velezd/pycogame/code/games/MicroMaze 3D/source/intro.png

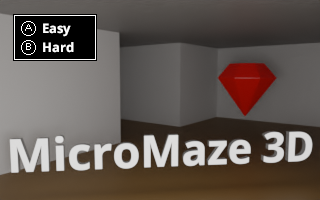
code/games/MicroMaze 3D/source/intro.png
