velezd/pycogame/code/games/MicroMaze 3D/source/graphics.png

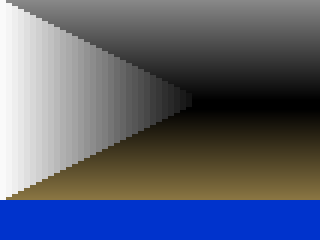
code/games/MicroMaze 3D/source/graphics.png
