velezd/pycogame/code/games/Micronoid/source/preview.png

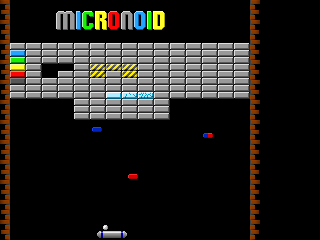
code/games/Micronoid/source/preview.png
