velezd/pycogame/code/games/MicroMaze 3D/maze.py

# -*- coding: utf-8 -*-
"""
Modified maze generator from BoppreH
https://github.com/boppreh/maze

The MIT License (MIT)

Copyright (c) 2014 BoppreH

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
# Easy to read representation for each cardinal direction.
N, S, W, E = ('n', 's', 'w', 'e')

class Cell(object):
    """
    Class for each individual cell. Knows only its position and which walls are
    still standing.
    """
    def __init__(self, x, y, walls):
        self.x = x
        self.y = y
        self.walls = set(walls)

    def __repr__(self):
        # <15, 25 (es  )>
        return '<{}, {} ({:4})>'.format(self.x, self.y, ''.join(sorted(self.walls)))

    def __contains__(self, item):
        # N in cell
        return item in self.walls

    def is_full(self):
        """
        Returns True if all walls are still standing.
        """
        return len(self.walls) == 4

    def _wall_to(self, other):
        """
        Returns the direction to the given cell from the current one.
        Must be one cell away only.
        """
        assert abs(self.x - other.x) + abs(self.y - other.y) == 1, '{}, {}'.format(self, other)
        if other.y < self.y:
            return N
        elif other.y > self.y:
            return S
        elif other.x < self.x:
            return W
        elif other.x > self.x:
            return E
        else:
            assert False

    def connect(self, other):
        """
        Removes the wall between two adjacent cells.
        """
        other.walls.remove(other._wall_to(self))
        self.walls.remove(self._wall_to(other))

class Maze(object):
    """
    Maze class containing full board and maze generation algorithms.
    """
    def __init__(self, width, height):
        """
        Creates a new maze with the given sizes, with all walls standing.
        """
        self.width = width
        self.height = height
        self.cells = []
        for y in range(self.height):
            for x in range(self.width):
                self.cells.append(Cell(x, y, [N, S, E, W]))

    def __getitem__(self, index):
        """
        Returns the cell at index = (x, y).
        """
        x, y = index
        if 0 <= x < self.width and 0 <= y < self.height:
            return self.cells[x + y * self.width]
        else:
            return None

    def neighbors(self, cell):
        """
        Returns the list of neighboring cells, not counting diagonals. Cells on
        borders or corners may have less than 4 neighbors.
        """
        x = cell.x
        y = cell.y
        for new_x, new_y in [(x, y - 1), (x, y + 1), (x - 1, y), (x + 1, y)]:
            neighbor = self[new_x, new_y]
            if neighbor is not None:
                yield neighbor

    def _to_str_matrix(self):
        """
        Returns a matrix with a pretty printed visual representation of this
        maze. Example 5x5:

        OOOOOOOOOOO
        O       O O
        OOO OOO O O
        O O   O   O
        O OOO OOO O
        O   O O   O
        OOO O O OOO
        O   O O O O
        O OOO O O O
        O     O   O
        OOOOOOOOOOO
        """
        str_matrix = [['#'] * (self.width * 2 + 1)
                      for i in range(self.height * 2 + 1)]

        for cell in self.cells:
            x = cell.x * 2 + 1
            y = cell.y * 2 + 1
            str_matrix[y][x] = '.'

            if N not in cell and y > 0:
                str_matrix[y - 1][x + 0] = '.'
            if S not in cell and y + 1 < self.width:
                str_matrix[y + 1][x + 0] = '.'
            if W not in cell and x > 0:
                str_matrix[y][x - 1] = '.'
            if E not in cell and x + 1 < self.width:
                str_matrix[y][x + 1] = '.'

        return str_matrix

    def randomize(self):
        """
        Knocks down random walls to build a random perfect maze.

        Algorithm from http://mazeworks.com/mazegen/mazetut/index.htm
        """
        cell_stack = []
        cell = choice(self.cells)
        n_visited_cells = 1

        while n_visited_cells < len(self.cells):
            neighbors = [c for c in self.neighbors(cell) if c.is_full()]
            if len(neighbors):
                neighbor = choice(neighbors)
                cell.connect(neighbor)
                cell_stack.append(cell)
                cell = neighbor
                n_visited_cells += 1
            else:
                cell = cell_stack.pop()

    @staticmethod
    def generate(width=20, height=10):
        """
        Returns a new random perfect maze with the given sizes.
        """
        m = Maze(width, height)
        m.randomize()
        return m

def generate_maze(width, height):
    return Maze.generate(width, height)._to_str_matrix()
